AnonymisedFox/XRSeat/CAD/Solidworks/GROUND.SLDPRT

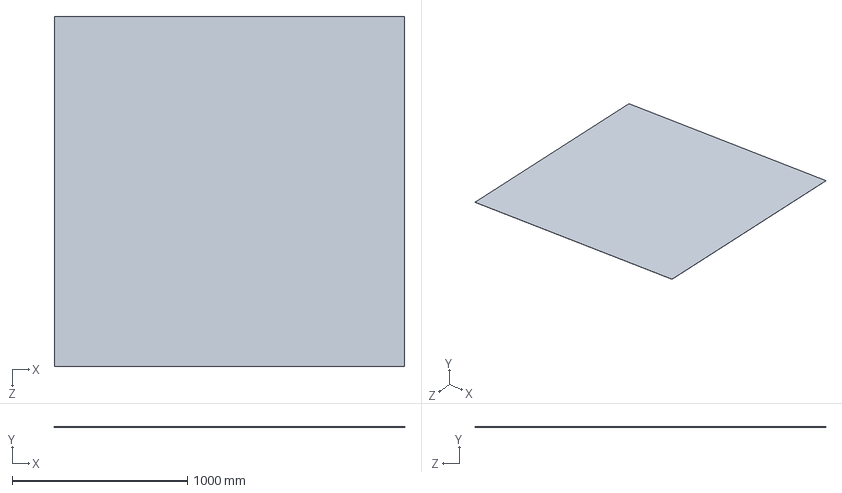
[picture p13: CAD file, 2026-01-21]
CAD/Solidworks/GROUND.SLDPRT
2000.0 x 1.00 x 2000.0 mm
