AnonymisedFox/XRSeat/CAD/Solidworks/GROUND_PART/ecrou_din934_m5-6.SLDPRT

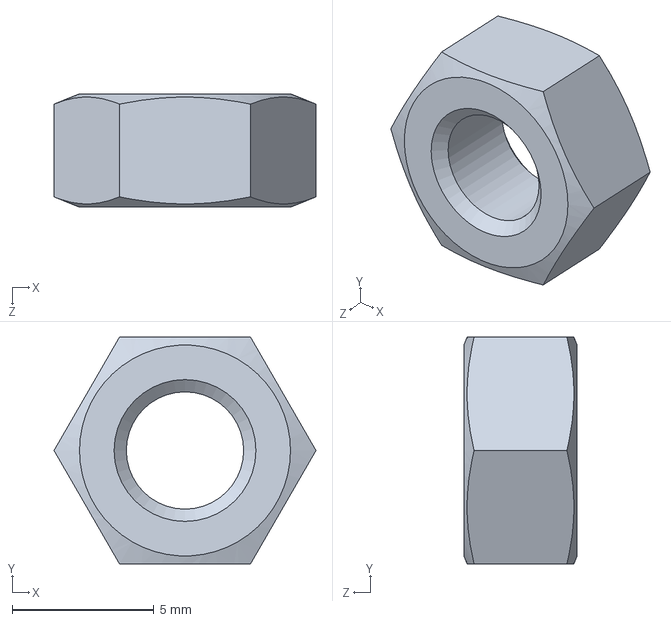
[picture p14: CAD file, 2026-01-21]
CAD/Solidworks/GROUND_PART/ecrou_din934_m5-6.SLDPRT
9.24 x 8.00 x 4.00 mm
