AnonymisedFox/XRSeat/CAD/Solidworks/HEAD_PART/WOODEN_BATTEN-2.SLDPRT

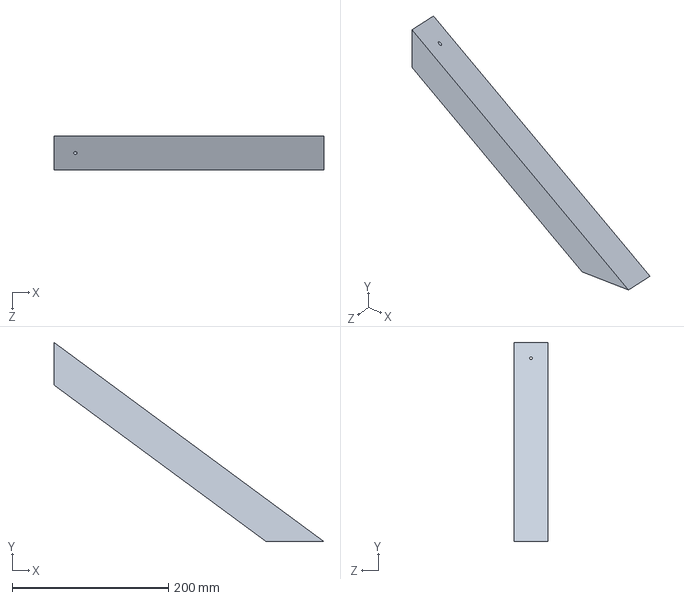
[picture p15: CAD file, 2026-01-21]
CAD/Solidworks/HEAD_PART/WOODEN_BATTEN-2.SLDPRT
346.0 x 255.3 x 44.0 mm
