AnonymisedFox/XRSeat/CAD/Solidworks/PROJECTION_PART/LACK_TABLE.SLDPRT

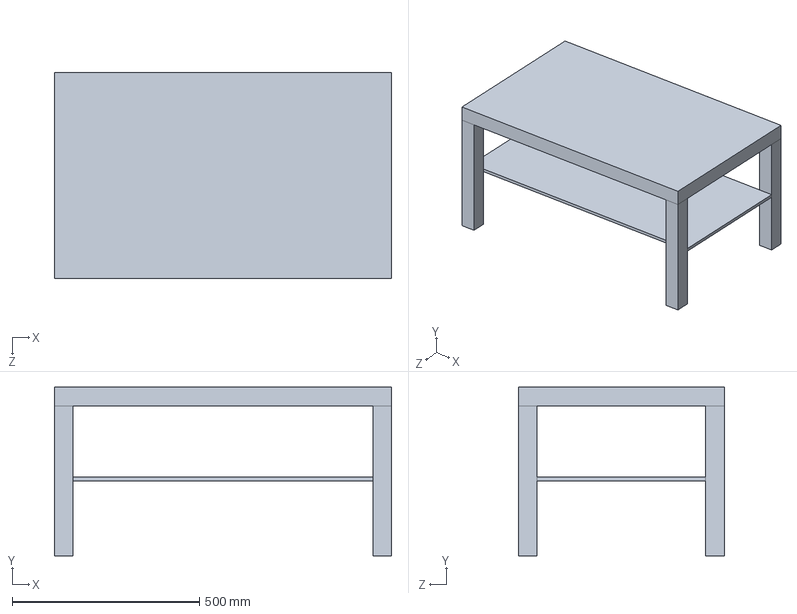
[picture p16: CAD file, 2026-01-21]
CAD/Solidworks/PROJECTION_PART/LACK_TABLE.SLDPRT
900.0 x 450.0 x 550.0 mm
