AnonymisedFox/XRSeat/CAD/Solidworks/ARMSET_PART/ARMSET-PLATE.SLDPRT

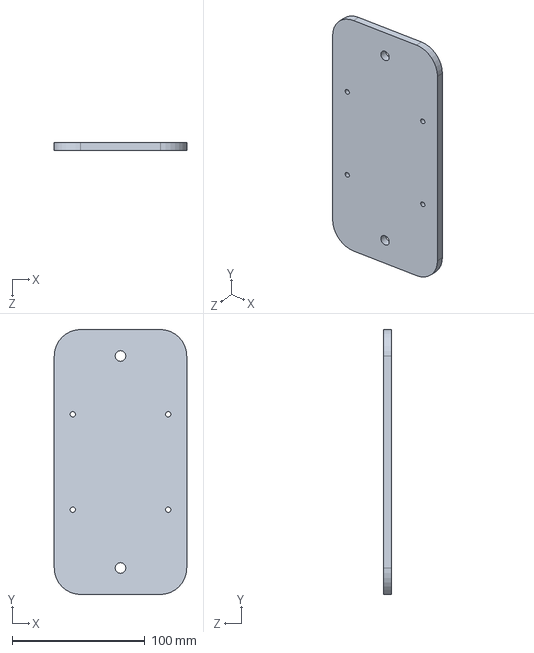
[picture p17: CAD file, 2026-01-21]
CAD/Solidworks/ARMSET_PART/ARMSET-PLATE.SLDPRT
100.0 x 200.0 x 6.00 mm
