AnonymisedFox/XRSeat/CAD/Solidworks/BACK_PART/ecrou_din934_m8-10.SLDPRT

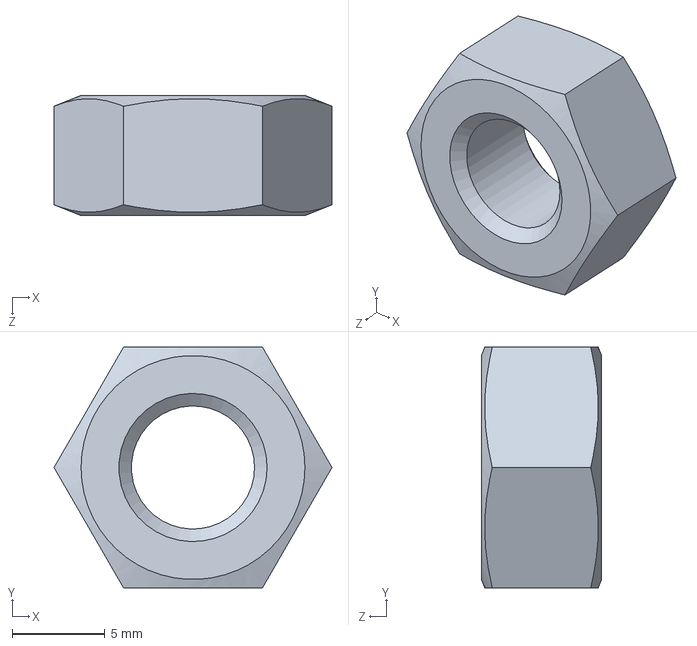
[picture p18: CAD file, 2026-01-21]
CAD/Solidworks/BACK_PART/ecrou_din934_m8-10.SLDPRT
15.0 x 13.0 x 6.50 mm
