AnonymisedFox/XRSeat/CAD/Solidworks/HEAD_PART/vis_iso_4017-m3x30-10_9.SLDPRT

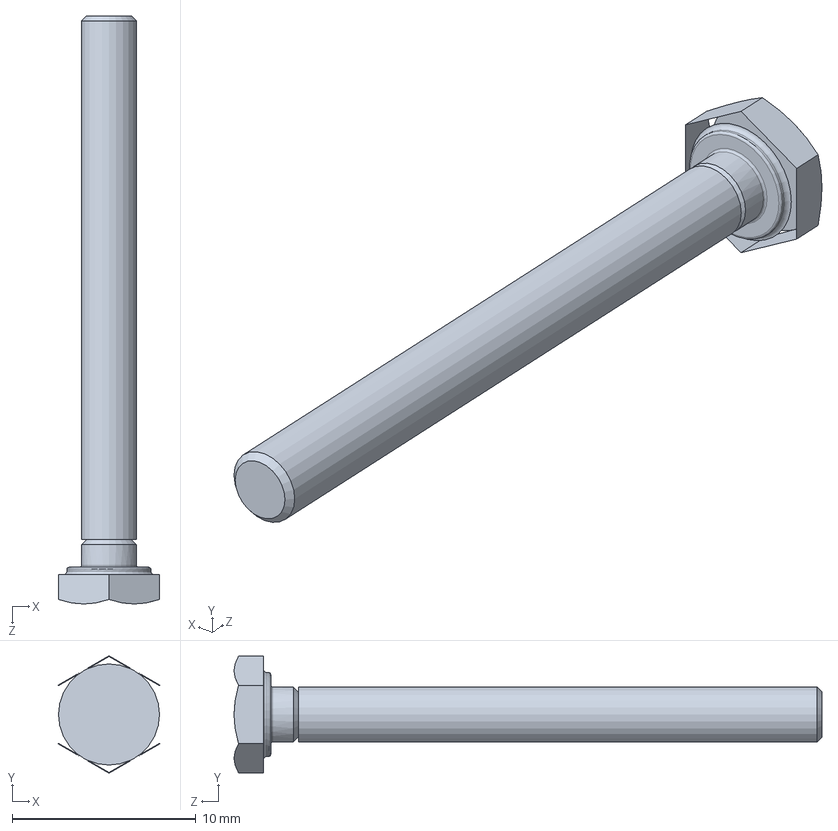
[picture p19: CAD file, 2026-01-21]
CAD/Solidworks/HEAD_PART/vis_iso_4017-m3x30-10_9.SLDPRT
5.50 x 6.35 x 32.0 mm
