AnonymisedFox/XRSeat/CAD/Solidworks/PROJECTION_PART/PROJECTION_BACK.SLDPRT

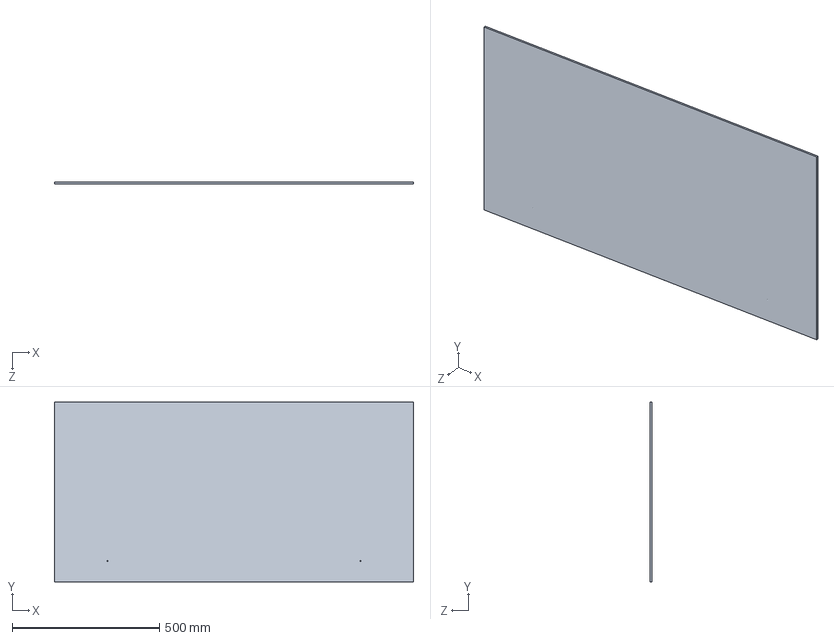
[picture p20: CAD file, 2026-01-21]
CAD/Solidworks/PROJECTION_PART/PROJECTION_BACK.SLDPRT
1220.0 x 610.0 x 6.00 mm
