AnonymisedFox/XRSeat/CAD/Solidworks/ARMSET_PART/vis_uni_5933_m8x40-10_9_0.SLDPRT

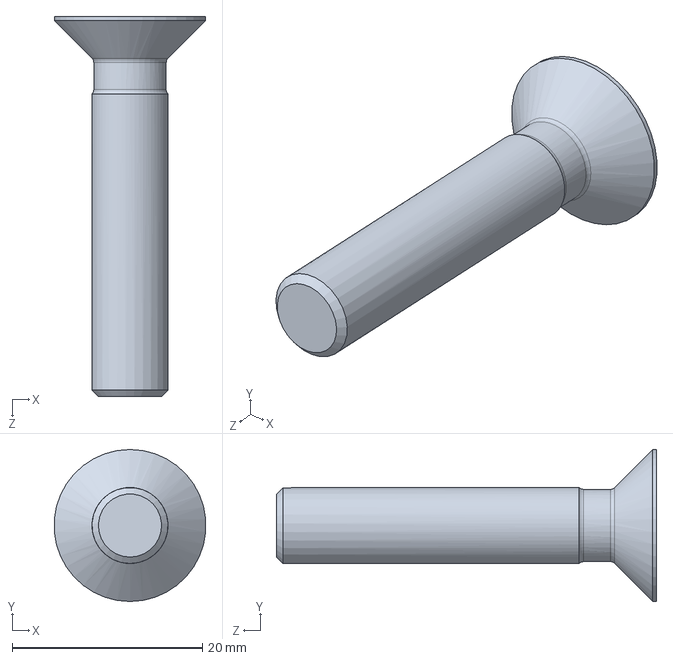
[picture p21: CAD file, 2026-01-21]
CAD/Solidworks/ARMSET_PART/vis_uni_5933_m8x40-10_9_0.SLDPRT
15.9 x 16.0 x 40.0 mm
