AnonymisedFox/XRSeat/CAD/Solidworks/BACK_PART/ecrou_din934_m4-6.SLDPRT

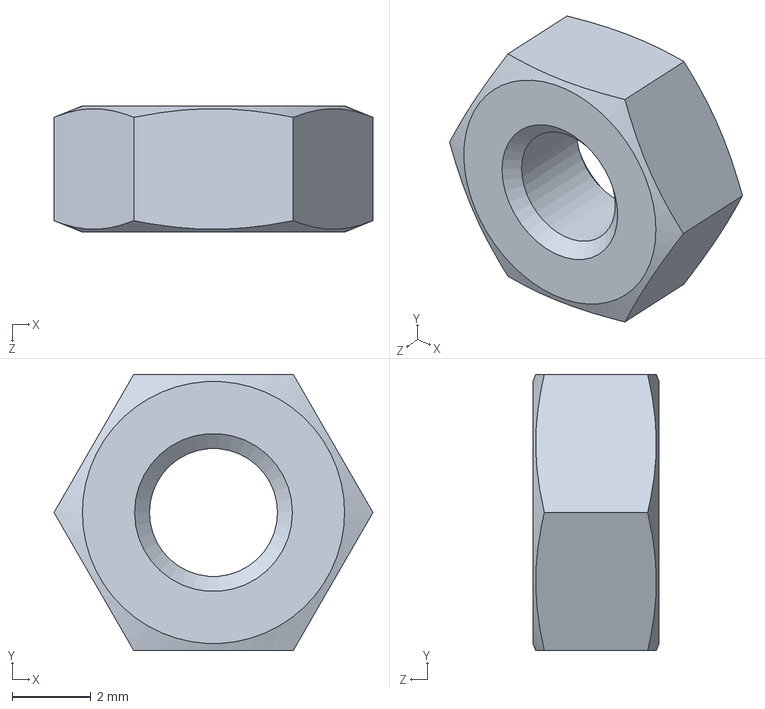
[picture p22: CAD file, 2026-01-21]
CAD/Solidworks/BACK_PART/ecrou_din934_m4-6.SLDPRT
8.08 x 7.00 x 3.20 mm
