AnonymisedFox/XRSeat/CAD/Solidworks/GROUND_PART/Visaton_EX_80_S.SLDPRT

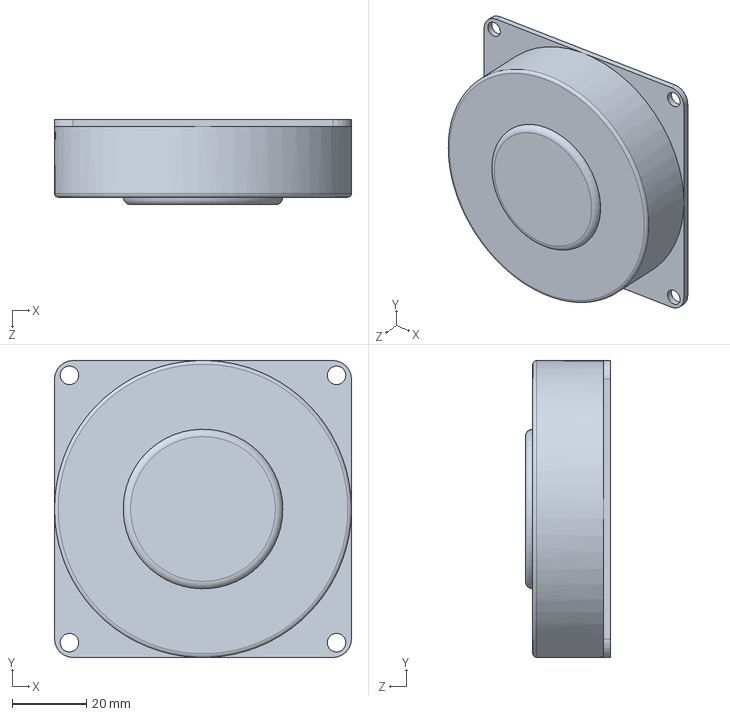
[picture p23: CAD file, 2026-01-21]
CAD/Solidworks/GROUND_PART/Visaton_EX_80_S.SLDPRT
80.0 x 80.0 x 23.0 mm
