AnonymisedFox/XRSeat/CAD/Solidworks/HEAD_PART/WOODEN_BATTEN-3.SLDPRT

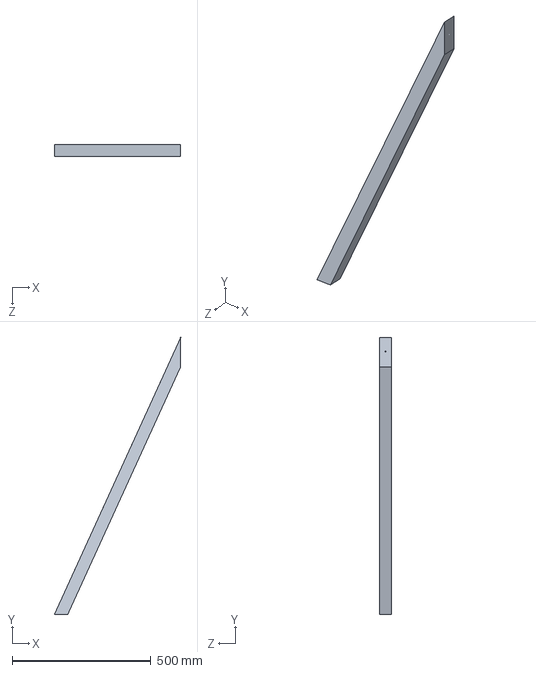
[picture p24: CAD file, 2026-01-21]
CAD/Solidworks/HEAD_PART/WOODEN_BATTEN-3.SLDPRT
456.0 x 1000.0 x 44.0 mm
