AnonymisedFox/XRSeat/CAD/Solidworks/GROUND_PART/din_en_24017_m5x30.SLDPRT

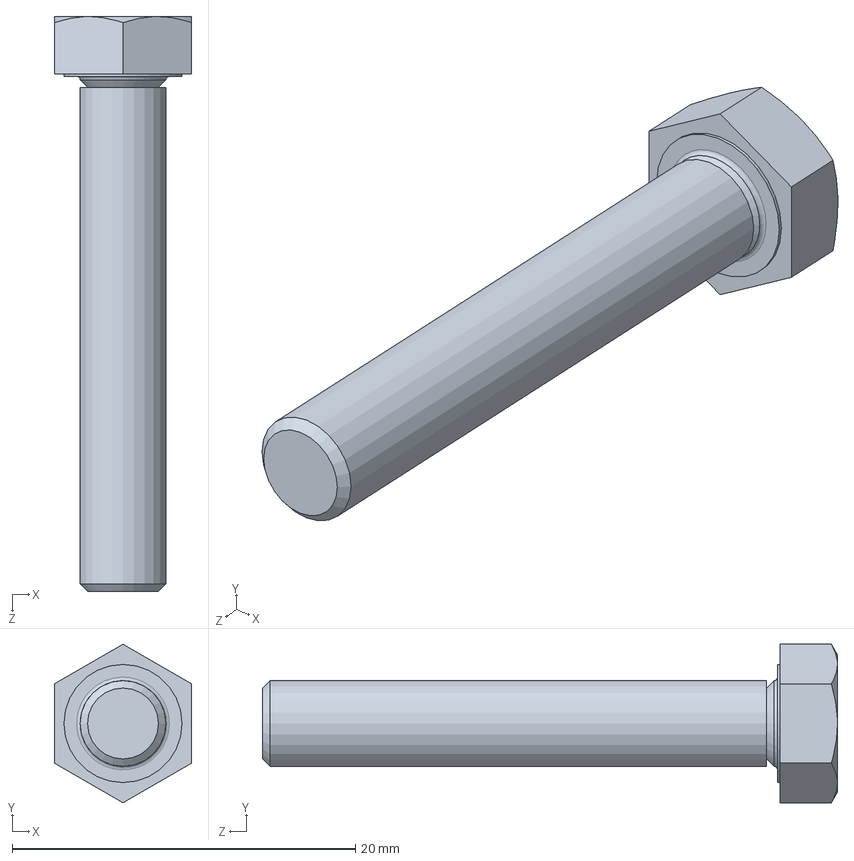
[picture p25: CAD file, 2026-01-21]
CAD/Solidworks/GROUND_PART/din_en_24017_m5x30.SLDPRT
8.00 x 9.24 x 33.5 mm
