AnonymisedFox/XRSeat/CAD/Solidworks/HEAD_PART/WOODEN_BATTEN-1.SLDPRT

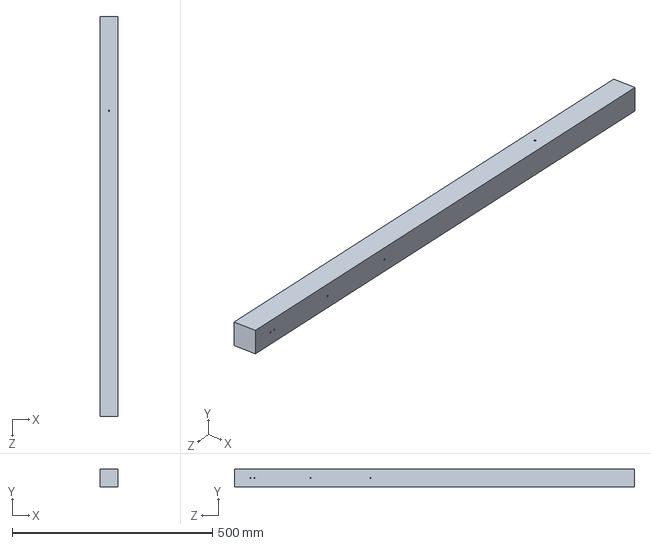
[picture p26: CAD file, 2026-01-21]
CAD/Solidworks/HEAD_PART/WOODEN_BATTEN-1.SLDPRT
44.0 x 44.0 x 1000.0 mm
