AnonymisedFox/XRSeat/CAD/Solidworks/BACK_PART/BACK-PLATE.SLDPRT

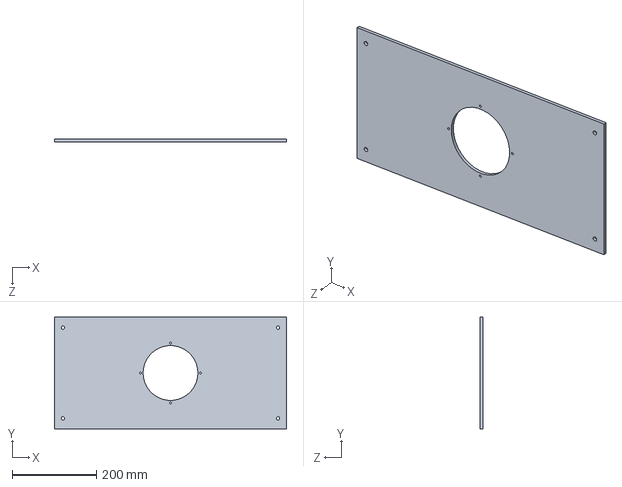
[picture p27: CAD file, 2026-01-21]
CAD/Solidworks/BACK_PART/BACK-PLATE.SLDPRT
550.0 x 265.0 x 6.00 mm
