AnonymisedFox/XRSeat/CAD/Solidworks/GROUND_PART/WOODEN_BATTEN-44X44_L506.SLDPRT

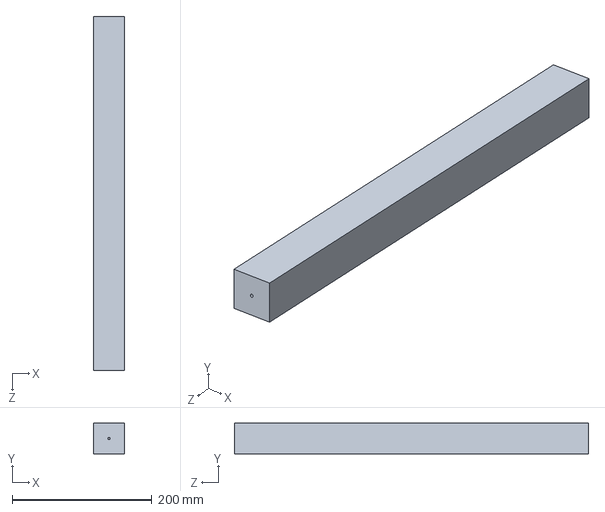
[picture p28: CAD file, 2026-01-21]
CAD/Solidworks/GROUND_PART/WOODEN_BATTEN-44X44_L506.SLDPRT
44.0 x 44.0 x 506.0 mm
