AnonymisedFox/XRSeat/CAD/Solidworks/GROUND_PART/Fiche_Visaton_EX_80_S.SLDPRT

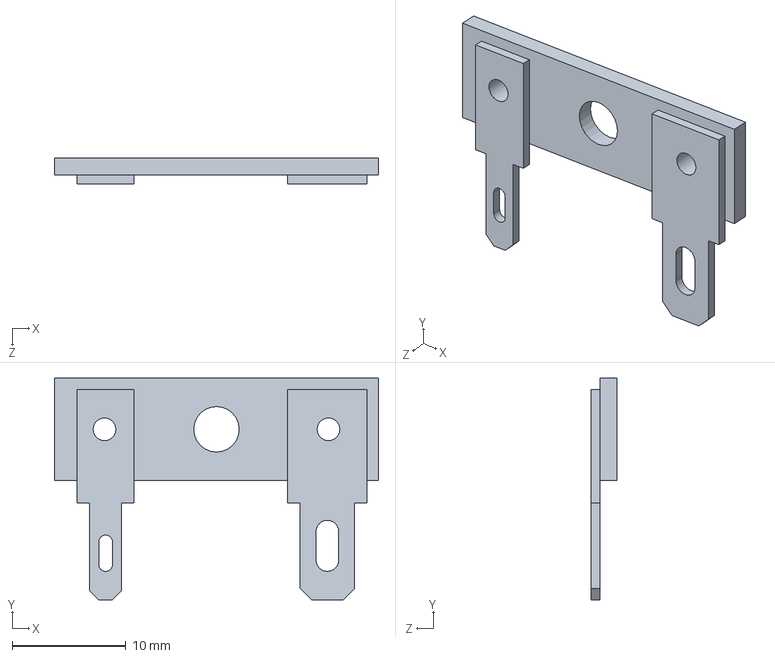
[picture p29: CAD file, 2026-01-21]
CAD/Solidworks/GROUND_PART/Fiche_Visaton_EX_80_S.SLDPRT
28.5 x 19.5 x 2.30 mm
