AnonymisedFox/XRSeat/CAD/Solidworks/GROUND_PART/WOODEN_BATTEN-44X44_L271.SLDPRT

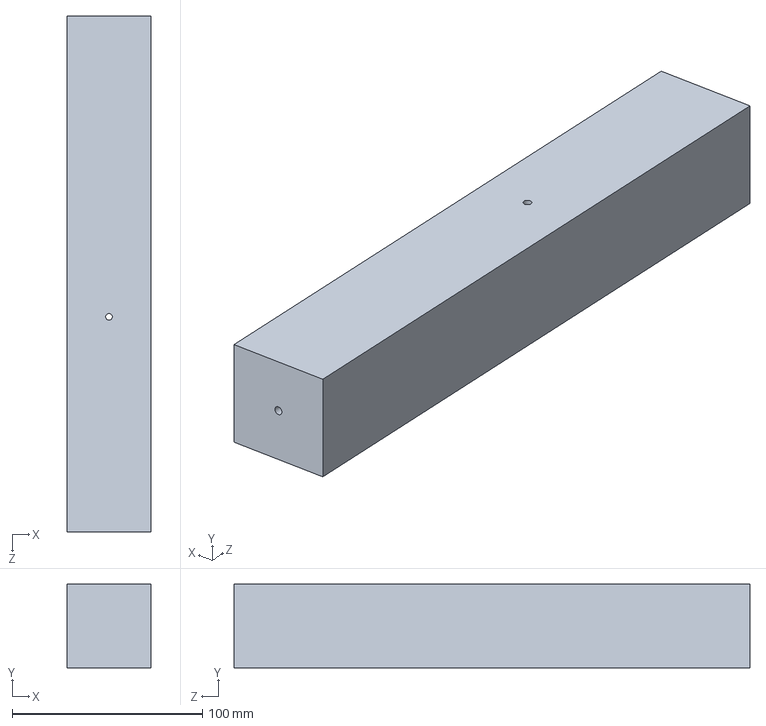
[picture p30: CAD file, 2026-01-21]
CAD/Solidworks/GROUND_PART/WOODEN_BATTEN-44X44_L271.SLDPRT
44.0 x 44.0 x 271.0 mm
