AnonymisedFox/XRSeat/CAD/Solidworks/HEAD_PART/RIGHT-EAR-Support_LED_P2.STL

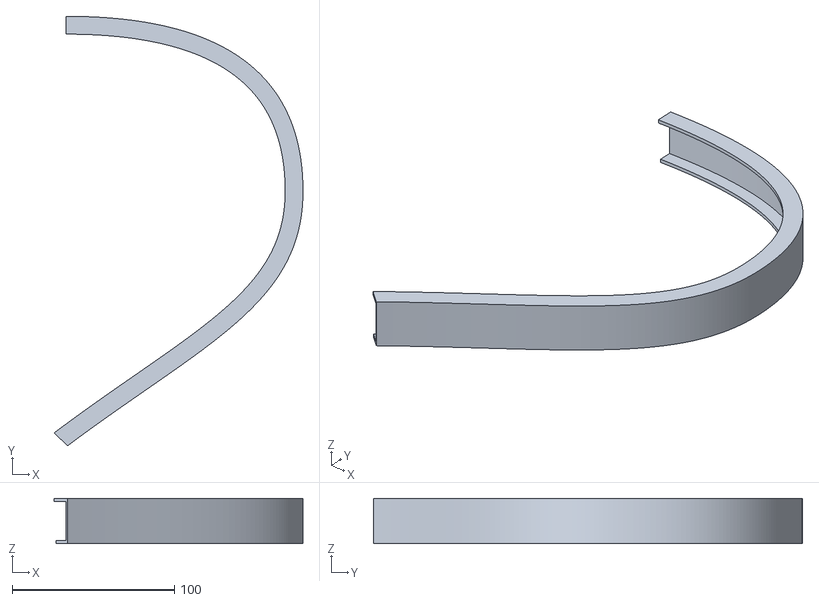
[picture p31: CAD file, 2026-01-21]
CAD/Solidworks/HEAD_PART/RIGHT-EAR-Support_LED_P2.STL
153.5 x 264.8 x 28.0
