AnonymisedFox/XRSeat/CAD/Step_Files/SubComponents/FR 58 Magnet.stp.STEP

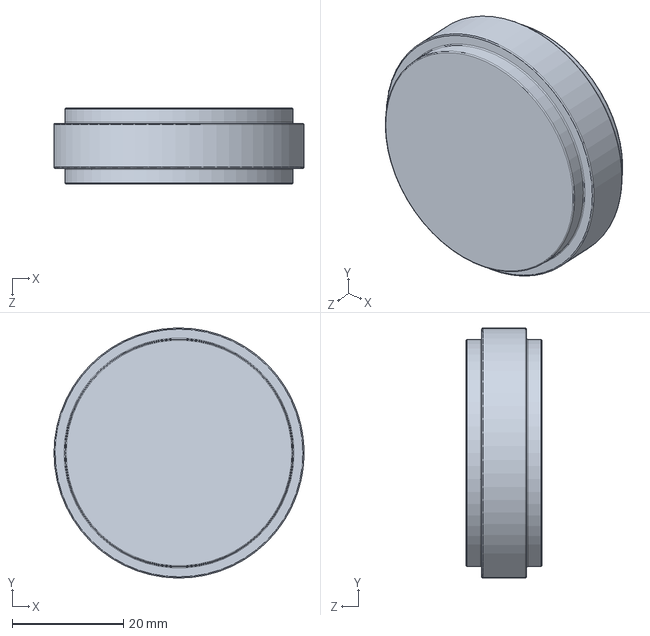
[picture p32: CAD file, 2026-01-21]
CAD/Step_Files/SubComponents/FR 58 Magnet.stp.STEP
45.0 x 45.0 x 13.7 mm
