AnonymisedFox/XRSeat/CAD/Solidworks/GROUND_PART/WOODEN_BATTEN-44X44_L650.SLDPRT

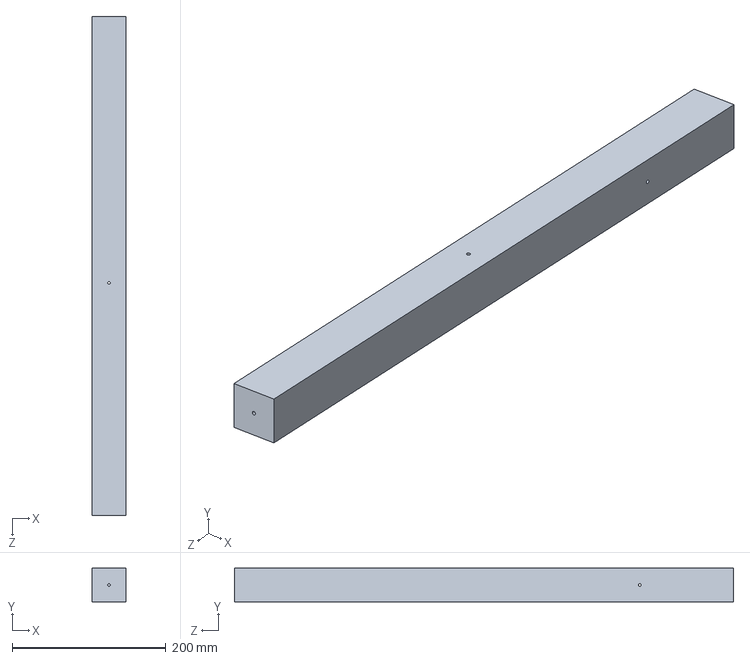
[picture p33: CAD file, 2026-01-21]
CAD/Solidworks/GROUND_PART/WOODEN_BATTEN-44X44_L650.SLDPRT
44.0 x 44.0 x 650.0 mm
