AnonymisedFox/XRSeat/CAD/Step_Files/SubComponents/vis_iso_4017-m3x30-10_9.STEP

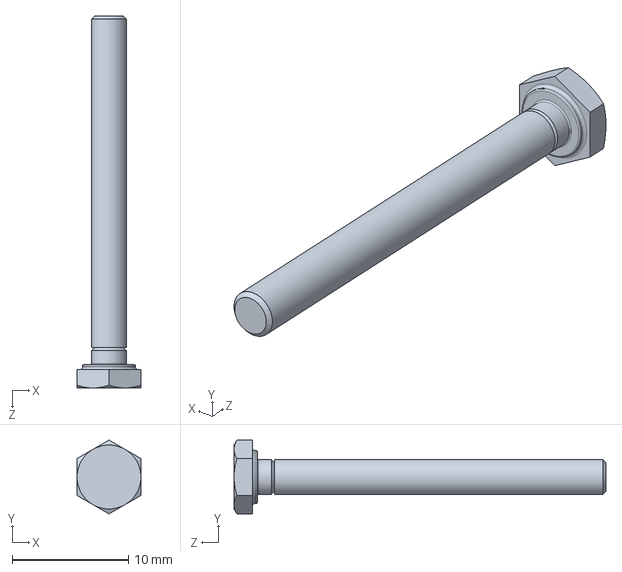
[picture p34: CAD file, 2026-01-21]
CAD/Step_Files/SubComponents/vis_iso_4017-m3x30-10_9.STEP
5.50 x 6.35 x 32.0 mm
