AnonymisedFox/XRSeat/CAD/Solidworks/GROUND_PART/WOODEN_BATTEN-44X44_L680.SLDPRT

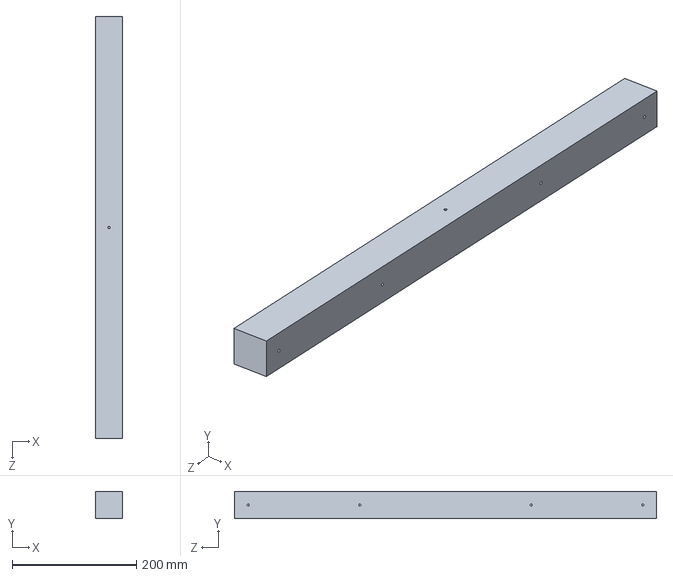
[picture p35: CAD file, 2026-01-21]
CAD/Solidworks/GROUND_PART/WOODEN_BATTEN-44X44_L680.SLDPRT
44.0 x 44.0 x 680.0 mm
