AnonymisedFox/XRSeat/CAD/Solidworks/HEAD_PART/Synjet_Plexi_TB.SLDPRT

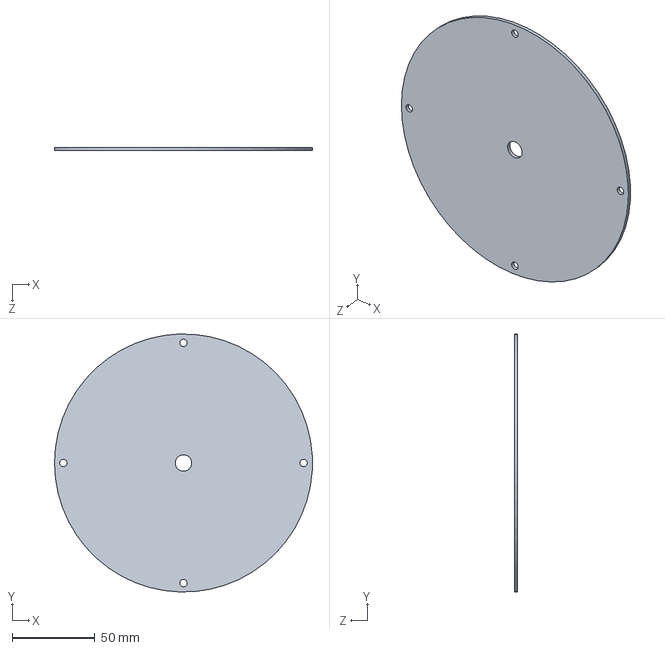
[picture p36: CAD file, 2026-01-21]
CAD/Solidworks/HEAD_PART/Synjet_Plexi_TB.SLDPRT
155.8 x 155.7 x 2.00 mm
