AnonymisedFox/XRSeat/CAD/Solidworks/HEAD_PART/EAR.SLDPRT

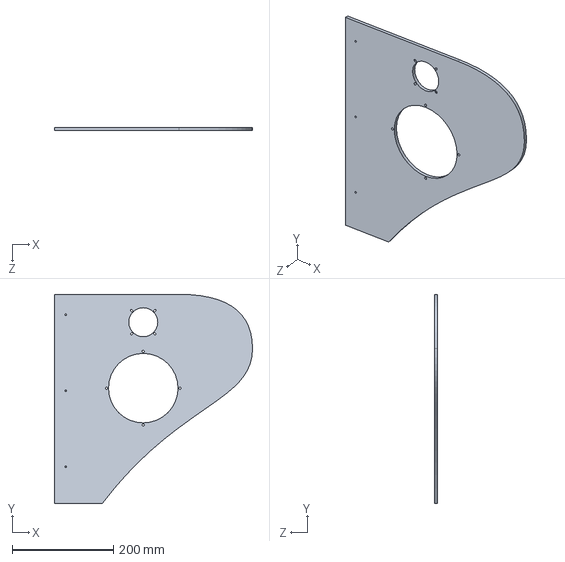
[picture p37: CAD file, 2026-01-21]
CAD/Solidworks/HEAD_PART/EAR.SLDPRT
390.4 x 412.8 x 6.00 mm
