AnonymisedFox/XRSeat/CAD/Step_Files/SubComponents/EX 80 S_part_1.STEP

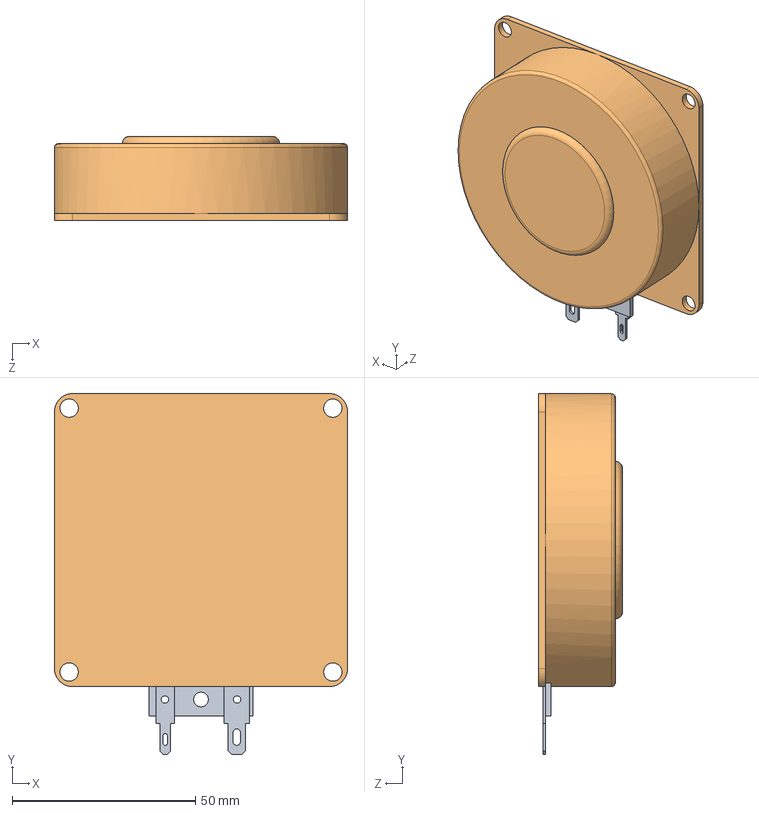
[picture p38: CAD file, 2026-01-21]
CAD/Step_Files/SubComponents/EX 80 S_part_1.STEP
80.0 x 98.5 x 23.0 mm
