AnonymisedFox/XRSeat/CAD/Solidworks/HEAD_PART/Synjet_Support_TB.SLDPRT

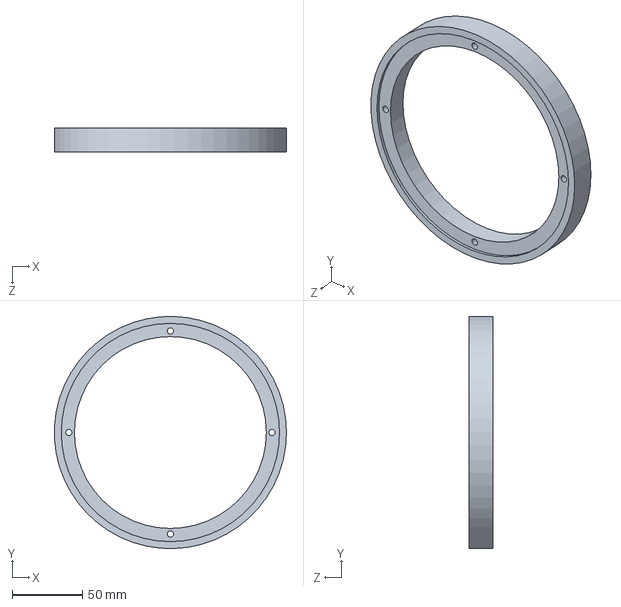
[picture p39: CAD file, 2026-01-21]
CAD/Solidworks/HEAD_PART/Synjet_Support_TB.SLDPRT
165.7 x 165.7 x 17.0 mm
