AnonymisedFox/XRSeat/CAD/Step_Files/SubComponents/FR 58 Membran und Sicke.stp.STEP

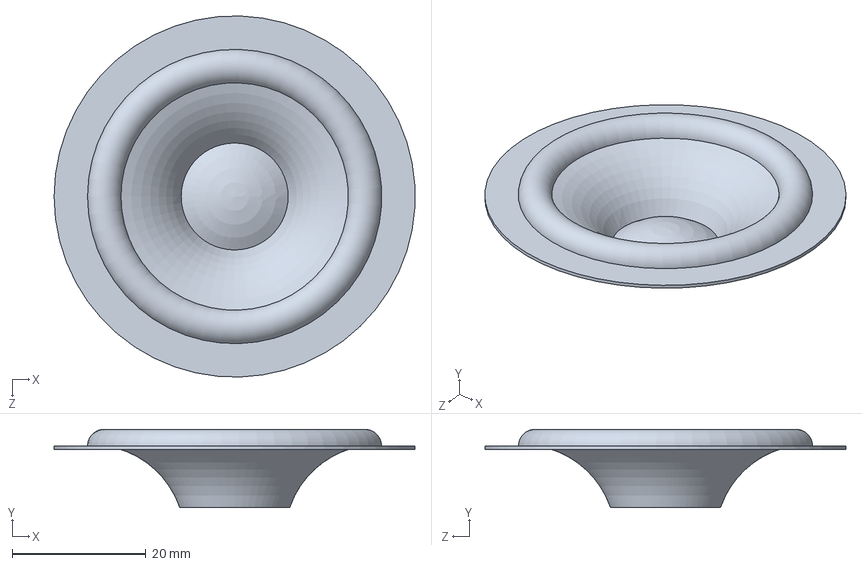
[picture p40: CAD file, 2026-01-21]
CAD/Step_Files/SubComponents/FR 58 Membran und Sicke.stp.STEP
53.9 x 11.7 x 54.0 mm
