AnonymisedFox/XRSeat/CAD/Step_Files/SubComponents/ARM_WOOD_P1.STEP

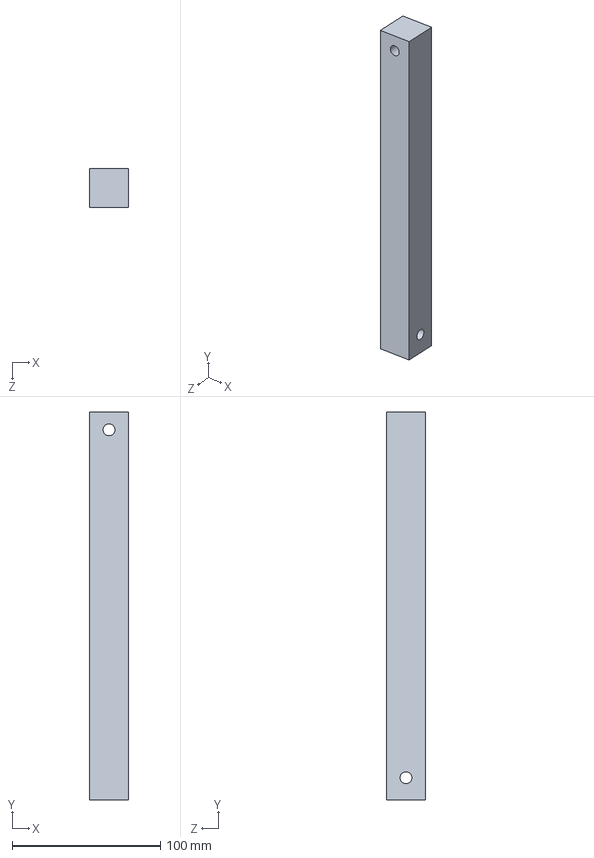
[picture p41: CAD file, 2026-01-21]
CAD/Step_Files/SubComponents/ARM_WOOD_P1.STEP
26.0 x 261.5 x 26.0 mm
