AnonymisedFox/XRSeat/CAD/Step_Files/SubComponents/ARM_WOOD_P2.STEP

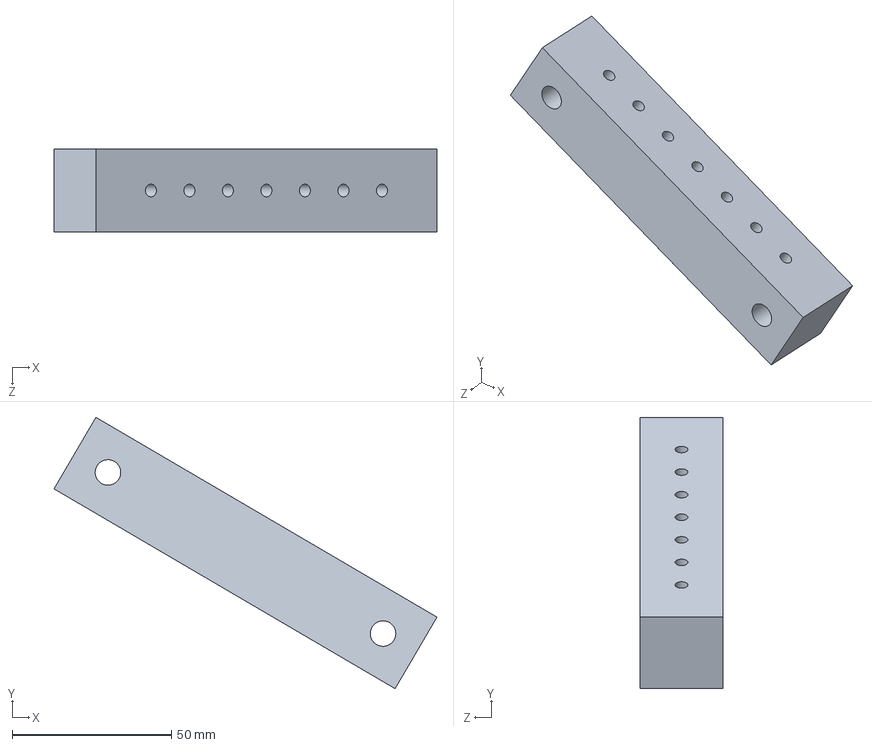
[picture p42: CAD file, 2026-01-21]
CAD/Step_Files/SubComponents/ARM_WOOD_P2.STEP
120.1 x 85.1 x 26.0 mm
