AnonymisedFox/XRSeat/CAD/Step_Files/SubComponents/INNER_SUPPORT.STEP

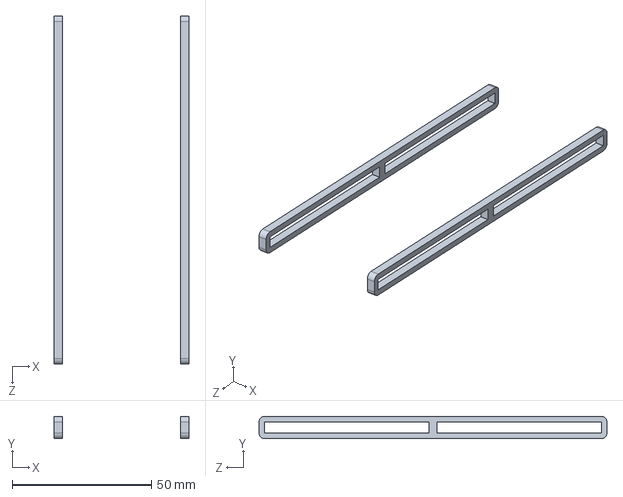
[picture p43: CAD file, 2026-01-21]
CAD/Step_Files/SubComponents/INNER_SUPPORT.STEP
48.5 x 8.00 x 125.0 mm
