AnonymisedFox/XRSeat/CAD/Step_Files/SubComponents/din_en_24017_m8x60.STEP

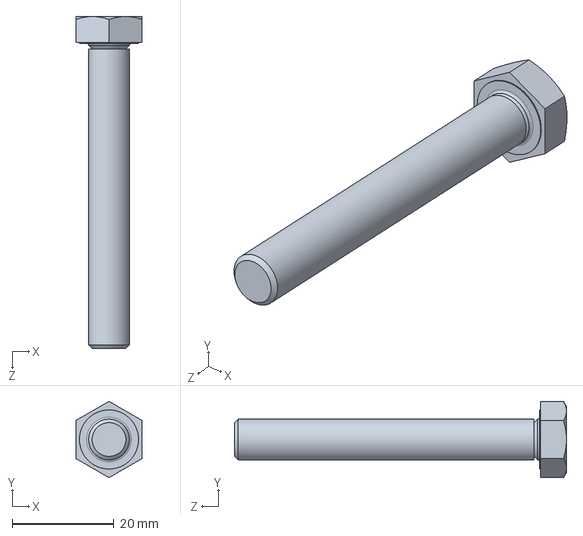
[picture p44: CAD file, 2026-01-21]
CAD/Step_Files/SubComponents/din_en_24017_m8x60.STEP
13.0 x 15.0 x 65.3 mm
