AnonymisedFox/XRSeat/CAD/Step_Files/SubComponents/_Terminalplatte 29 x 9,2 x 1,6.stp.STEP

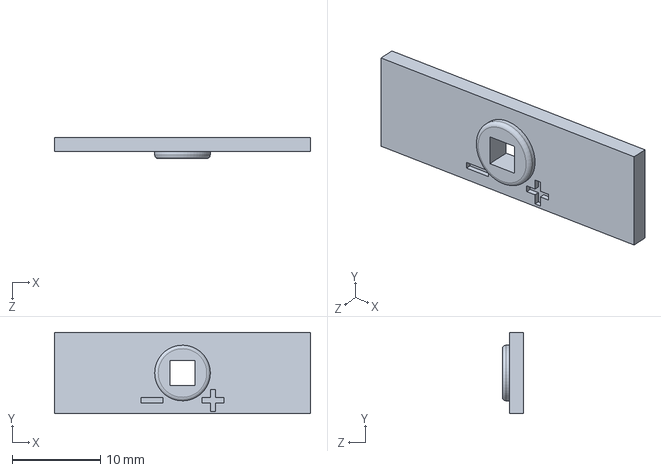
[picture p45: CAD file, 2026-01-21]
CAD/Step_Files/SubComponents/_Terminalplatte 29 x 9,2 x 1,6.stp.STEP
29.0 x 9.20 x 2.40 mm
