AnonymisedFox/XRSeat/CAD/Step_Files/SubComponents/FR 58 Korb.stp.STEP

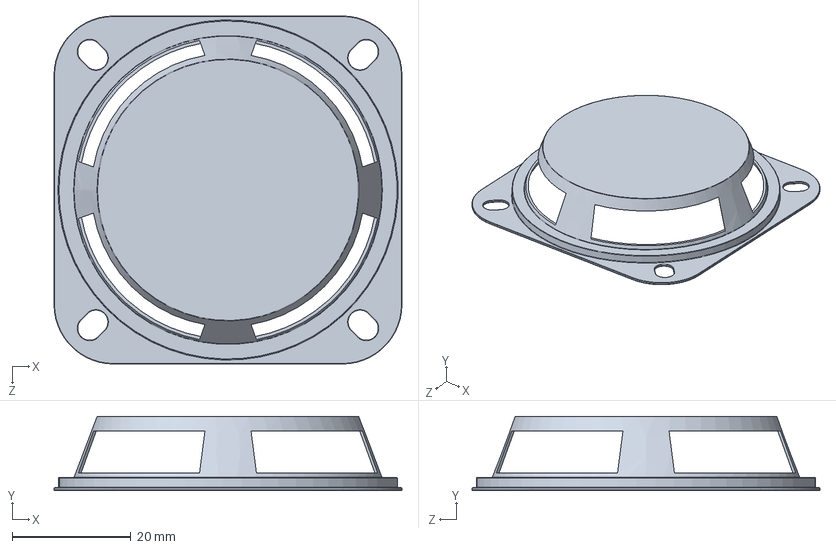
[picture p46: CAD file, 2026-01-21]
CAD/Step_Files/SubComponents/FR 58 Korb.stp.STEP
58.5 x 12.5 x 58.5 mm
