AnonymisedFox/XRSeat/CAD/Step_Files/SubComponents/SIDE_SUPPORT.STEP

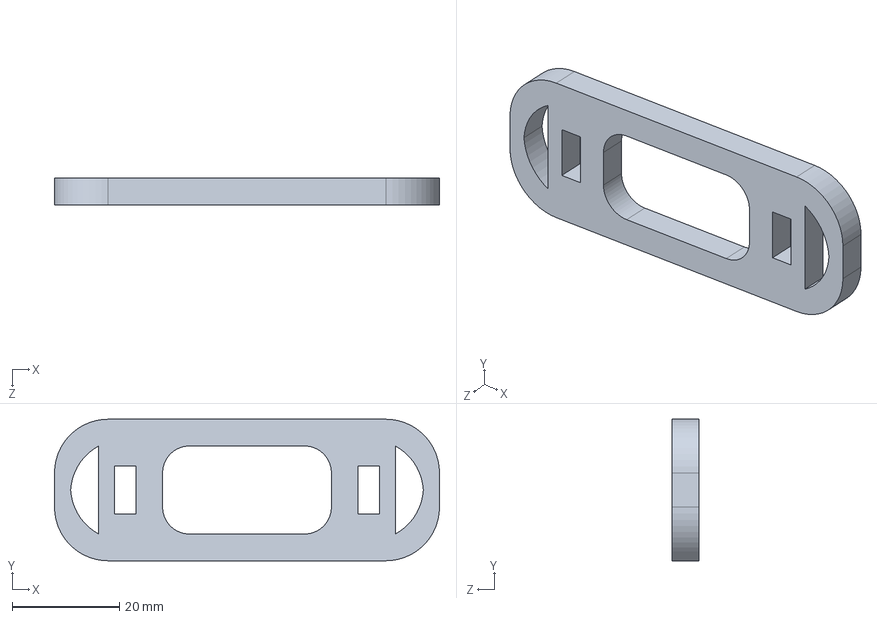
[picture p47: CAD file, 2026-01-21]
CAD/Step_Files/SubComponents/SIDE_SUPPORT.STEP
71.9 x 26.4 x 5.00 mm
