AnonymisedFox/XRSeat/CAD/Step_Files/SubComponents/BSX 130 WP metal body.stp.STEP

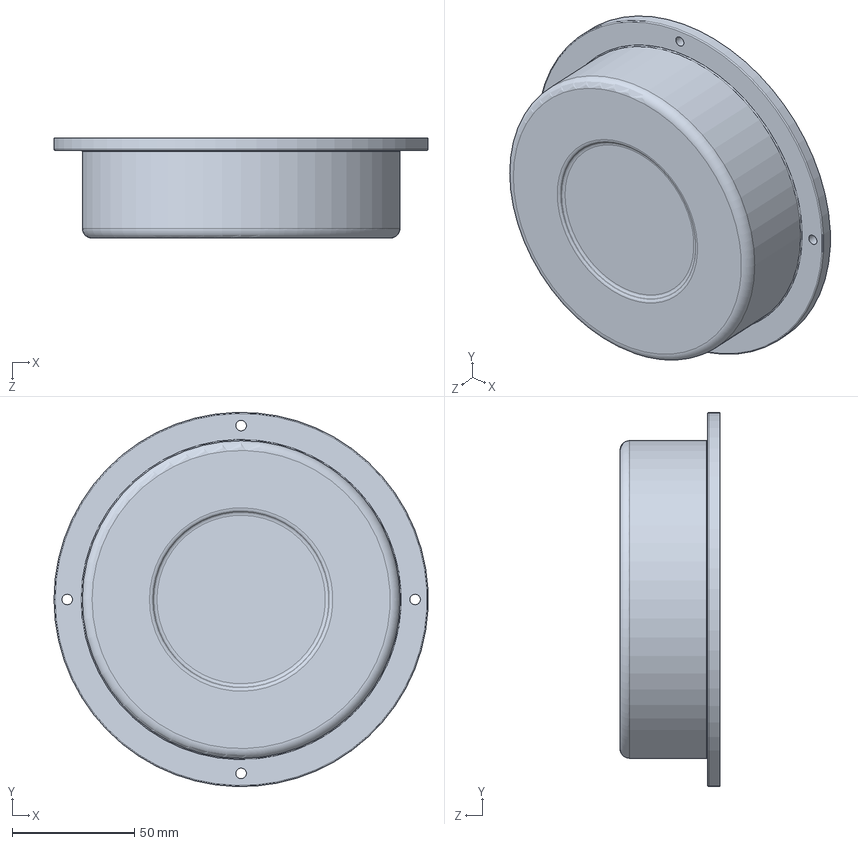
[picture p48: CAD file, 2026-01-21]
CAD/Step_Files/SubComponents/BSX 130 WP metal body.stp.STEP
152.7 x 152.7 x 40.9 mm
