AnonymisedFox/XRSeat/CAD/Step_Files/SubComponents/Dämpfung.stp.STEP

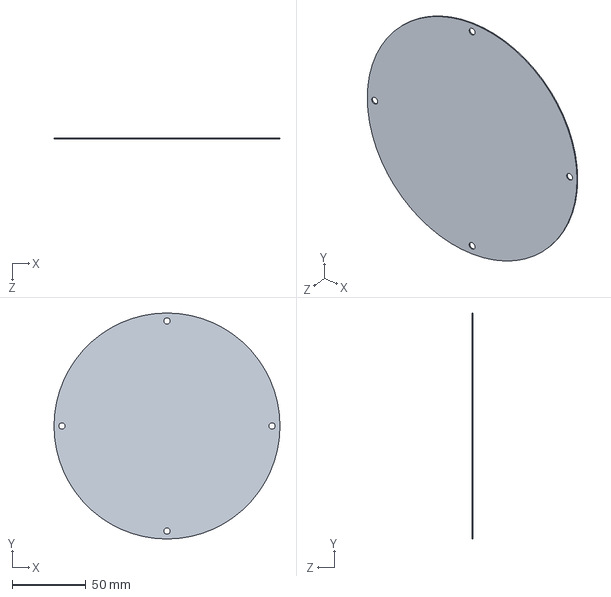
[picture p49: CAD file, 2026-01-21]
CAD/Step_Files/SubComponents/Dämpfung.stp.STEP
152.8 x 152.8 x 0.7 mm
