AnonymisedFox/XRSeat/CAD/Step_Files/SubComponents/_Terminal 5.2-0.5 (135°).stp.STEP

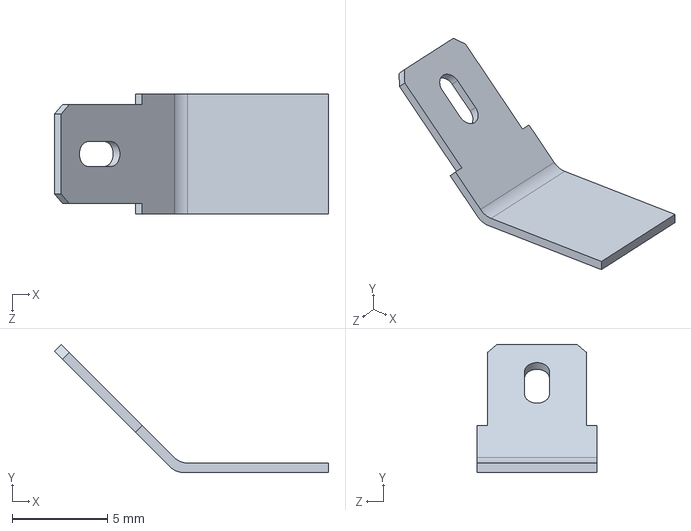
[picture p50: CAD file, 2026-01-21]
CAD/Step_Files/SubComponents/_Terminal 5.2-0.5 (135°).stp.STEP
14.4 x 6.72 x 6.30 mm
