AnonymisedFox/XRSeat/CAD/Step_Files/SubComponents/TOP_SUPPORT.STEP

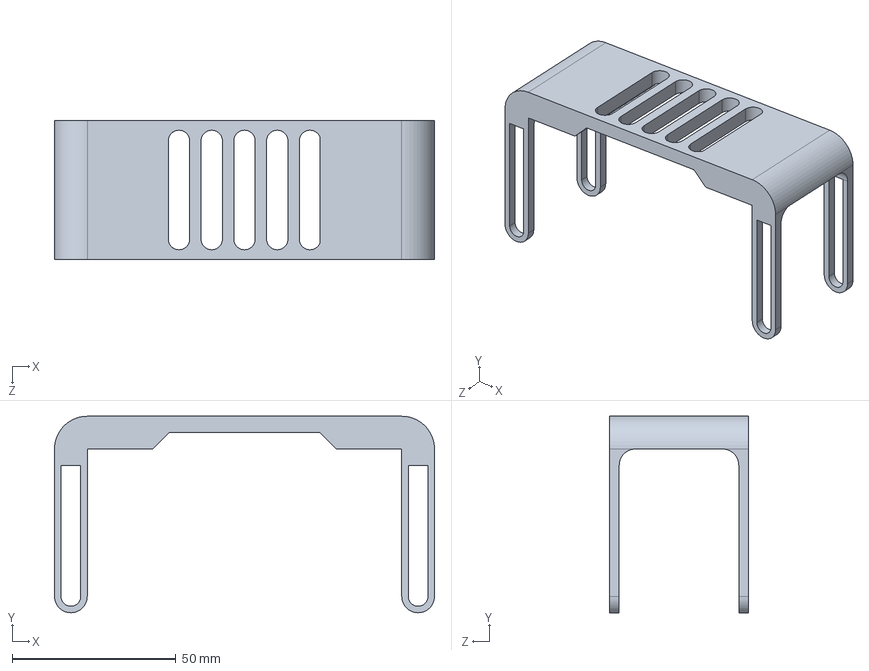
[picture p51: CAD file, 2026-01-21]
CAD/Step_Files/SubComponents/TOP_SUPPORT.STEP
116.0 x 60.0 x 42.5 mm
