AnonymisedFox/XRSeat/CAD/Step_Files/SubComponents/INOVASENS.STEP

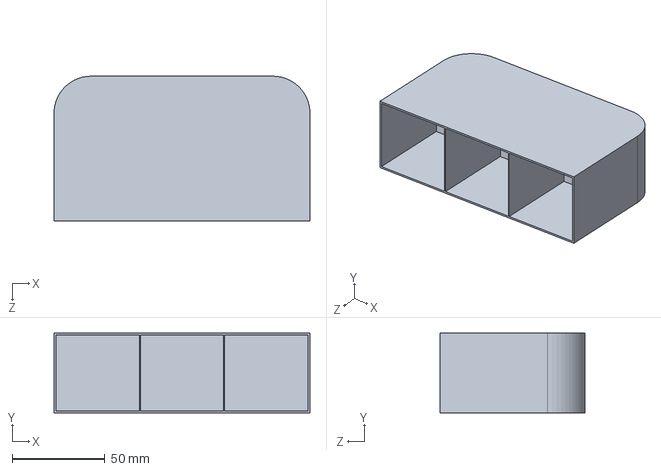
[picture p52: CAD file, 2026-01-21]
CAD/Step_Files/SubComponents/INOVASENS.STEP
138.0 x 43.0 x 78.0 mm
