AnonymisedFox/XRSeat/CAD/Step_Files/SubComponents/_Terminal 2.8-0.5 (135°) 2.stp.STEP

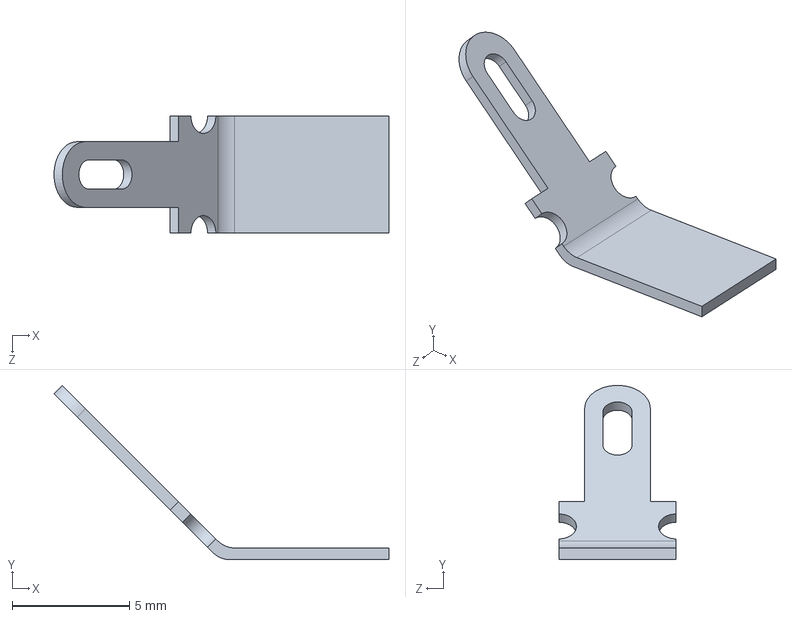
[picture p53: CAD file, 2026-01-21]
CAD/Step_Files/SubComponents/_Terminal 2.8-0.5 (135°) 2.stp.STEP
14.3 x 7.42 x 5.00 mm
