AnonymisedFox/XRSeat/CAD/Step_Files/SubComponents/FR 58 Gummidichtring.stp.STEP

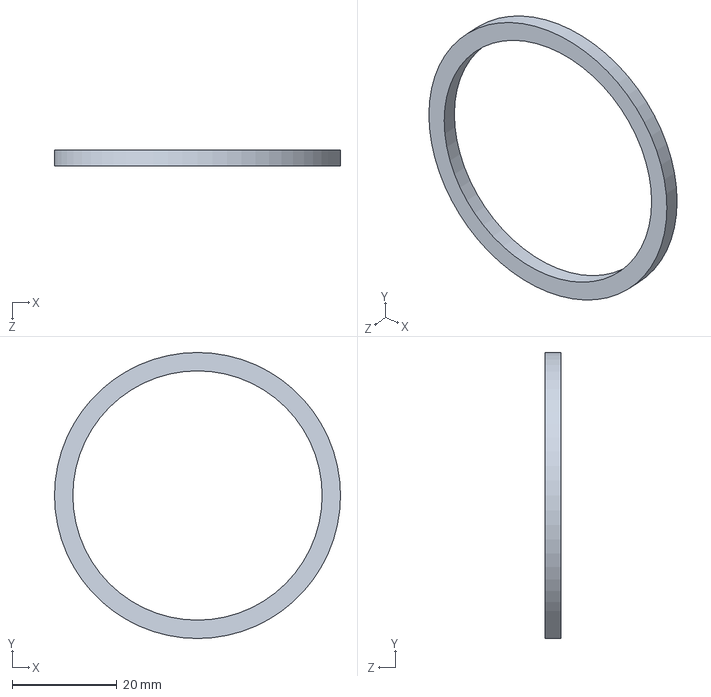
[picture p54: CAD file, 2026-01-21]
CAD/Step_Files/SubComponents/FR 58 Gummidichtring.stp.STEP
54.5 x 54.5 x 3.00 mm
